max-yip/MTRX2700_Group3_ThursAM_Final_Assignment/CAD/sensor_box_pic.png

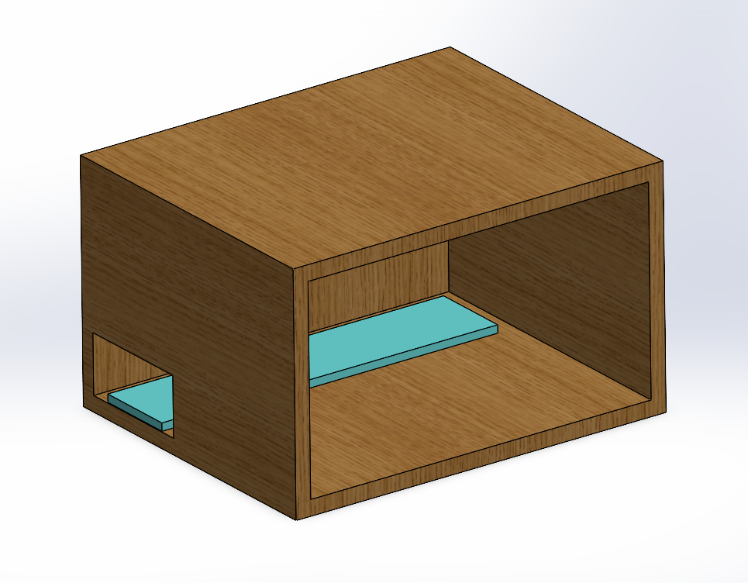
CAD/sensor_box_pic.png
