max-yip/MTRX2700_Group3_ThursAM_Final_Assignment/code/puzzle_major_project/Core/Inc/servo.h

/*
 * servo.h
 *
 *  Created on: May 14, 2025
 *      Author: shuvayu
 */

#ifndef INC_SERVO_H_
#define INC_SERVO_H_

#include <stdint.h>
#include "stm32f303xc.h"

extern void (*on_button_press)();
void enable_clocks(void);
void enableGPIOAButton();
void enable_interrupt();
void Servo_Init(void);

void rotate_servo_90();

#endif /* INC_SERVO_H_ */
