max-yip/MTRX2700_Group3_ThursAM_Final_Assignment/code/modules and interfaces/major_project_ldr/Src/gpio.c

/*
 * gpio.c
 *
 *  Created on: May 19, 2025
 *      Author: maxyi
 */

#include <stdint.h>
#include "stm32f303xc.h"
#include "timer.h"

/* layout of file:
 *
 * - Definitions
 * - GPIO clock enable
 * - GPIO configuration
 * - configuring specfic GPIO functions
 * 		- Specific register set ups
 * - Initialise Interrupts
 * - Initialise Interrupt Handler
 * - MISC functionality
 * - Major Initialise
 */

#define BUTTONPRIORITY 1 // CAN BE CHANGED

void (*onButtonPress)() = 0x00;


// ---------- CLOCK ENABLE ----------


void enableGPIOClocks() {
	RCC->AHBENR |= RCC_AHBENR_GPIOAEN | RCC_AHBENR_GPIOCEN | RCC_AHBENR_GPIODEN | RCC_AHBENR_GPIOEEN; // Enable GPIO A, C, D and E
	return;
}


// ---------- GPIO CONFIG ----------


void enableGPIOAButton() {
	GPIOA->MODER &= ~(0x3 << (0 * 2));
	return;
}

// set PE 0-6 to external leds
void enableGPIOELEDS() {
	// Set PE0–PE6 to General Purpose Output mode (MODER = 01)
	uint16_t *MODER = ((uint16_t *)&(GPIOE->MODER)) + 1;
	*MODER = 0x5555;
	return;
}

void enableGPIODLEDS() {
    // Set PD1, PD2, PD3 as output mode (01)
    GPIOD->MODER &= ~((0x3 << (1 * 2)) | (0x3 << (2 * 2)) | (0x3 << (3 * 2)));  // Clear bits
    GPIOD->MODER |=  ((0x1 << (1 * 2)) | (0x1 << (2 * 2)) | (0x1 << (3 * 2)));  // Set to output
}


// ---------- SPECIFIC GPIO E CONFIG ----------

// > LED ACCESS <

void setLEDState(uint8_t led_mask) {
	uint8_t *ODR = ((uint8_t*)&(GPIOE->ODR)) + 1;
	*ODR = led_mask;
	return;
}

uint8_t getLEDState() {
	uint8_t ODR = *((uint8_t*)&(GPIOE->ODR)) + 1;
	return ODR;
}

void setButtonCallback(void (*cb)(void)) {
	onButtonPress = cb;
}


// ----------- SPECIFIC GPIO D CONFIG ----------
// GPIOD set bits
void setRed(){
	GPIOD->ODR &= ~((1 << 2) | (1 << 3)); // turn off green and blue
	GPIOD->ODR |=  (1 << 1);              // turn on red
}

void setGreen(){
	GPIOD->ODR &= ~((1 << 1) | (1 << 3)); // turn off green and blue
	GPIOD->ODR |=  (1 << 2);              // turn on red
}

void setBlue(){
	GPIOD->ODR &= ~((1 << 1) | (1 << 2)); // turn off green and blue
	GPIOD->ODR |=  (1 << 3);              // turn on red
}


// ---------- INTERUPT ENABLE ----------

void enableButtonInterrupt() {
	// Disable the interrupts while messing around with the settings
	__disable_irq();

	RCC->APB2ENR |= RCC_APB2ENR_SYSCFGEN; // Enable the system configuration controller (SYSCFG in RCC)
	SYSCFG->EXTICR[0] = SYSCFG_EXTICR1_EXTI0_PA; /*
	* External Interrupts details on large manual page 294)
	* PA0 is on interrupt EXTI0 large manual - page 250
	* EXTI0 in  SYSCFG_EXTICR1 needs to be 0x00 (SYSCFG_EXTICR1_EXTI0_PA)
	*/
	EXTI->RTSR |= EXTI_RTSR_TR0; // Select EXTI0 interrupt on rising edge
	EXTI->IMR |= EXTI_IMR_MR0; // set the interrupt from EXTI line 0 as 'not masked' - as in, enable it.
	NVIC_SetPriority(EXTI0_IRQn, BUTTONPRIORITY); // Set Priority
	NVIC_EnableIRQ(EXTI0_IRQn); // Tell the NVIC module that EXTI0 interrupts should be handled

	__enable_irq(); // Re-enable all interrupts (now that we are finished)
	return;
}

// ---------- INTERUPT HANDLER ----------

void EXTI0_IRQHandler() {
	// run the button press handler (make sure it is not null first !)
	if (onButtonPress) {
		onButtonPress();
	}

	EXTI->PR |= EXTI_PR_PR0; // reset the interrupt
	return;
}

// ---------- MISC ----------

void chaseLed(){
	uint8_t led_register = getLEDState();

	/* If nothing lit, seed the pattern with the lowest LED */
	if (led_register == 0) led_register = 0x01;

	/* Rotate the entire pattern one step to the left */
	led_register = (led_register << 1) | (led_register >> 7);

	/* Write the new pattern to the LED driver */
	setLEDState(led_register);
}

void pendingChaseLed(){
	uint8_t led_register = getLEDState();

	/* If nothing lit, seed the pattern with the lowest LED */
	if (led_register == 0) led_register = 0x01;

	/* Rotate the entire pattern one step to the left */
	led_register = (led_register << 1) | (led_register >> 7);

	/* Write the new pattern to the LED driver */
	set_pending_bit_mask(led_register);
}


// ---------- MAJOR INIT ----------


void init_GPIO_ALL(void (*cb)(void)) {
	enableGPIOClocks();
	enableGPIOAButton();
	enableGPIOELEDS();
	enableGPIODLEDS();
	enableButtonInterrupt();
	EXTI0_IRQHandler();
	setButtonCallback(cb);
}
