max-yip/MTRX2700_Group3_ThursAM_Final_Assignment/code/major_project_lightsaber/Core/Inc/colour_detector.h

/*
 * colour_detector.h
 *
 *  Created on: May 20, 2025
 *      Author: maxyi
 */

#ifndef COLOUR_DETECTOR_H_
#define COLOUR_DETECTOR_H_

#include "serial.h"
#include "gpio.h"
#include "adc.h"
#include "i2c.h"


// State Machine
typedef enum {
    STATE_SET_RED, // set led to red
    STATE_READ_RED, // read ldr adc
    STATE_SET_GREEN, // set led to green
    STATE_READ_GREEN, // read ldr adc
    STATE_SET_BLUE, // set led to blue
    STATE_READ_BLUE, // read ldr adc
	STATE_CALIBRATION,
    STATE_DETERMINE_COLOUR, // determine colour
    STATE_TRANSMIT // output (currently its transmit through serial)
} ColorDetectState;

// colour type 1 = red, 2 = green
typedef enum {
    NO_COLOUR = 0,
    RED = 1,
    GREEN = 2
} ColourType;

// allow user access to detected colour
extern ColourType detectedColour;

//callback function for time to run the state machine
void handleStateMachine(void);


#endif /* COLOUR_DETECTOR_H_ */
