max-yip/MTRX2700_Group3_ThursAM_Final_Assignment/code/major_project_ptu/Core/Inc/ptu_i2c.h

/*
 * ptu_i2c.h
 *
 *  Created on: Apr 14, 2023
 *      Author: stew
 */

#ifndef INC_PTU_I2C_H_
#define INC_PTU_I2C_H_

#include "stm32f3xx_hal.h"
#include "serial.h"
#include "ptu_definitions.h"
#include <string.h>
#include <ctype.h>

//extern int16_t yaw_rate;
//extern int16_t pitch_rate;
//extern int16_t roll_rate;
//// get accel data
//extern int16_t acc_x;
//extern int16_t acc_y;
//extern int16_t acc_z;

void initialise_ptu_i2c(I2C_HandleTypeDef *i2c);

void read_gyro_data (I2C_HandleTypeDef *i2c, int16_t *yaw, int16_t *pitch, int16_t *roll);

void read_accel_data(I2C_HandleTypeDef *i2c, int16_t *acc_x, int16_t *acc_y, int16_t *acc_z);

void get_gyro_accel(I2C_HandleTypeDef *i2c,
                    int16_t* yaw_rate, int16_t* pitch_rate, int16_t* roll_rate,
                    int16_t* acc_x, int16_t* acc_y, int16_t* acc_z);

#endif /* INC_PTU_I2C_H_ */
