max-yip/MTRX2700_Group3_ThursAM_Final_Assignment/code/major_project_ptu/Core/Inc/ptu_lidar.h

/*
 * ptu_lidar.h
 *
 *  Created on: May 3, 2025
 *      Author: maxyi
 */

#ifndef INC_PTU_LIDAR_H_
#define INC_PTU_LIDAR_H_

#include "stm32f3xx_hal.h"
#include "serial.h"
#include "ptu_definitions.h"

extern uint16_t last_period;


#endif /* INC_PTU_LIDAR_H_ */
